zeeblaze/Melodio-SelfMate/Melodio_renders/R5.png

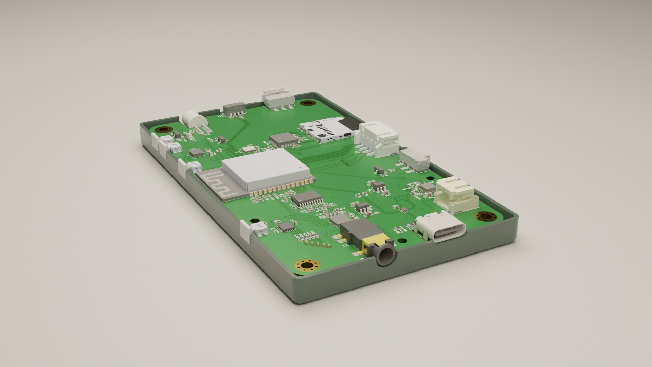
Melodio_renders/R5.png
