zeeblaze/Melodio-SelfMate/Melodio_renders/R6.png

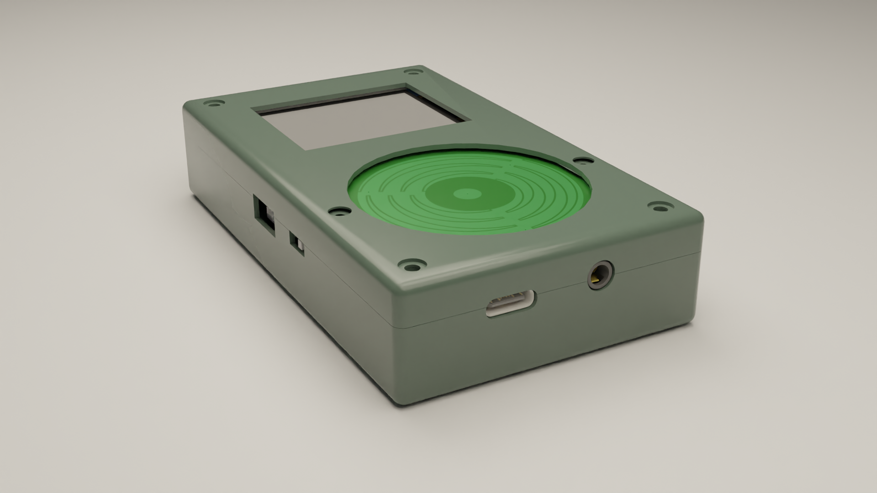
Melodio_renders/R6.png
