zeeblaze/Melodio-SelfMate/Melodio_renders/R7.png

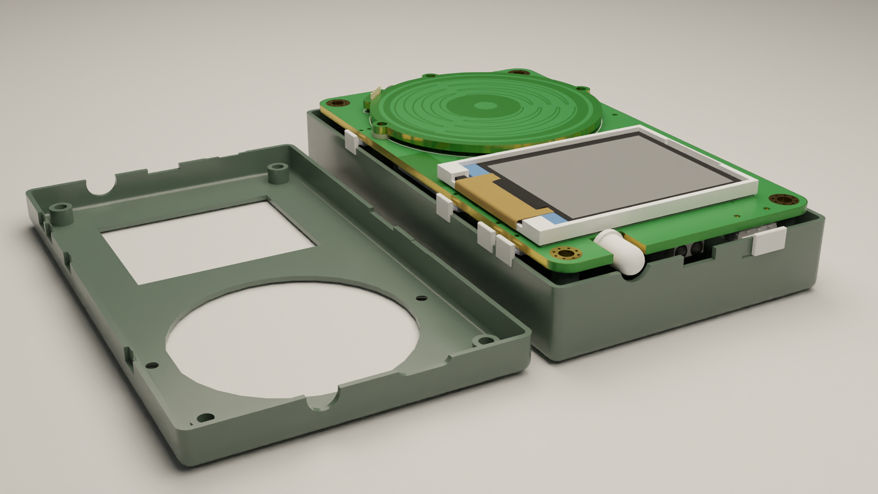
Melodio_renders/R7.png
