zeeblaze/Melodio-SelfMate/Output_PNGs/clickwheel_F_Cu.png

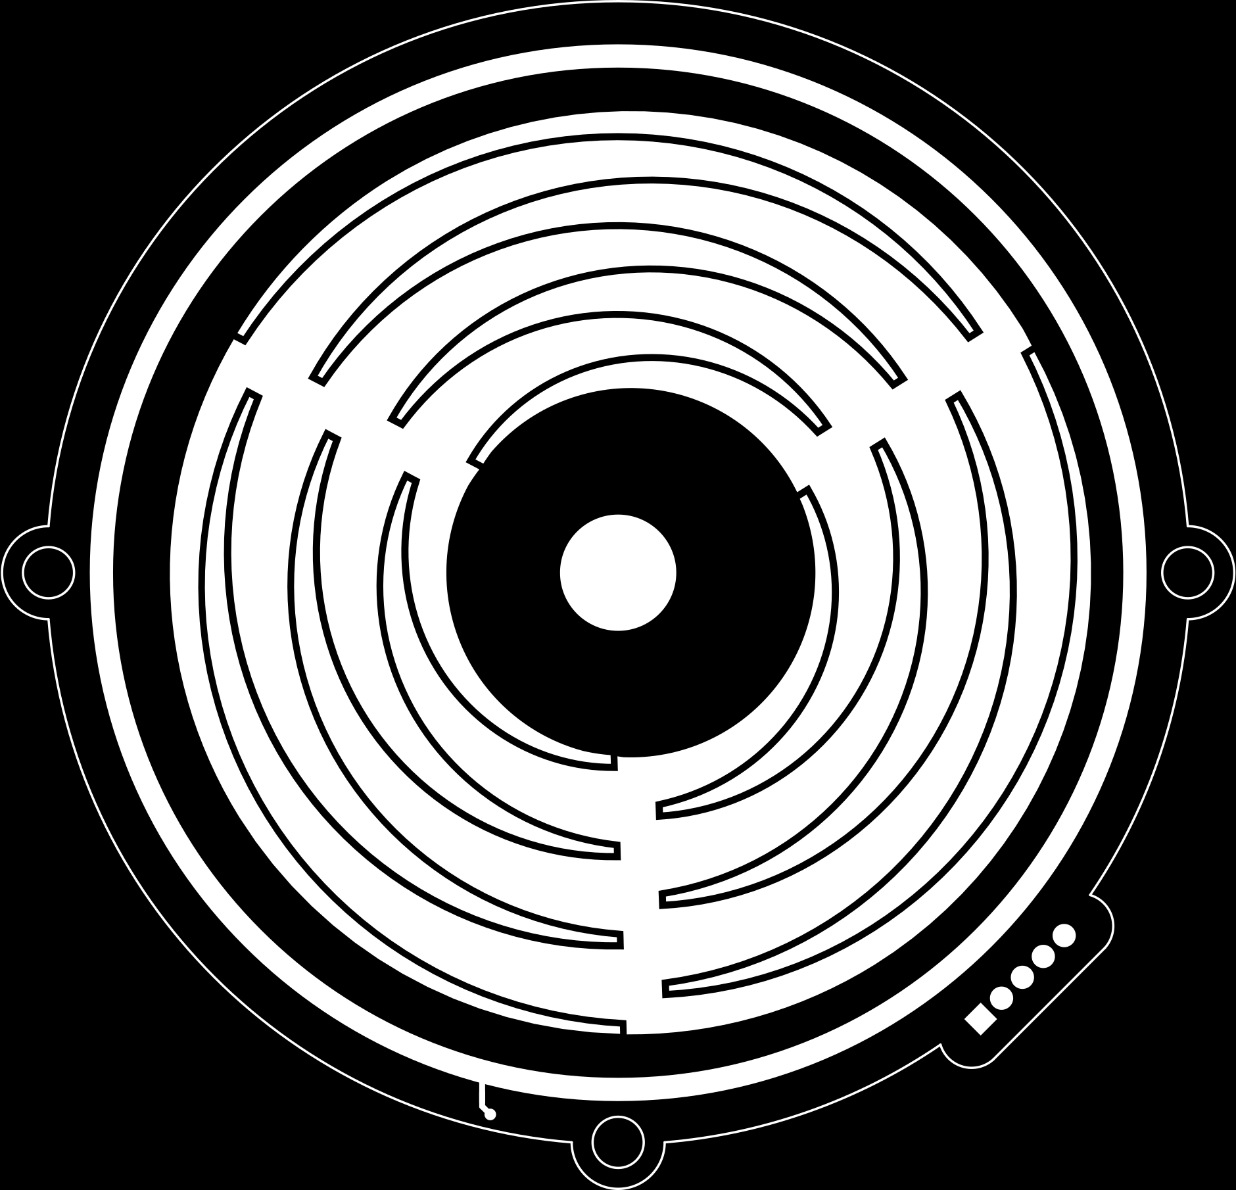
Output_PNGs/clickwheel_F_Cu.png
