zeeblaze/Melodio-SelfMate/Output_PNGs/clickwheel_F_Mask.png

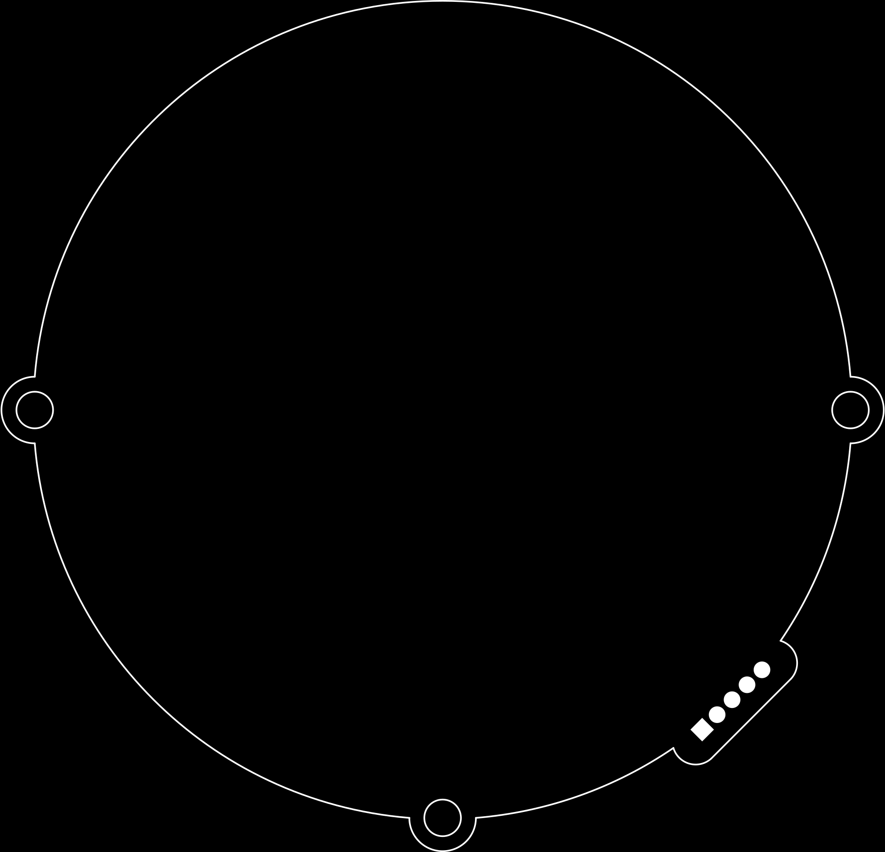
Output_PNGs/clickwheel_F_Mask.png
