zeeblaze/Melodio-SelfMate/Output_PNGs/pcb_B_Mask.png

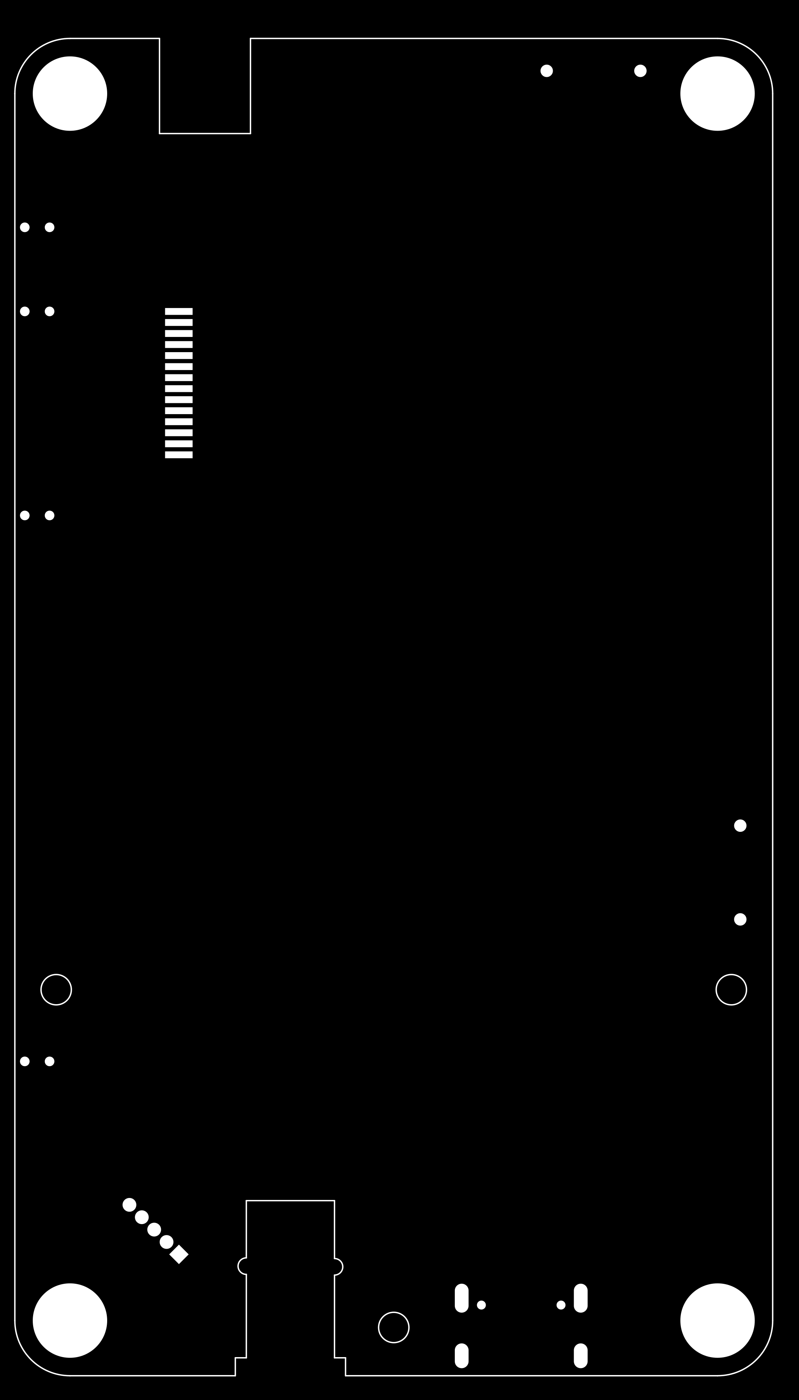
Output_PNGs/pcb_B_Mask.png
