zeeblaze/Melodio-SelfMate/Output_PNGs/pcb_F_Mask.png

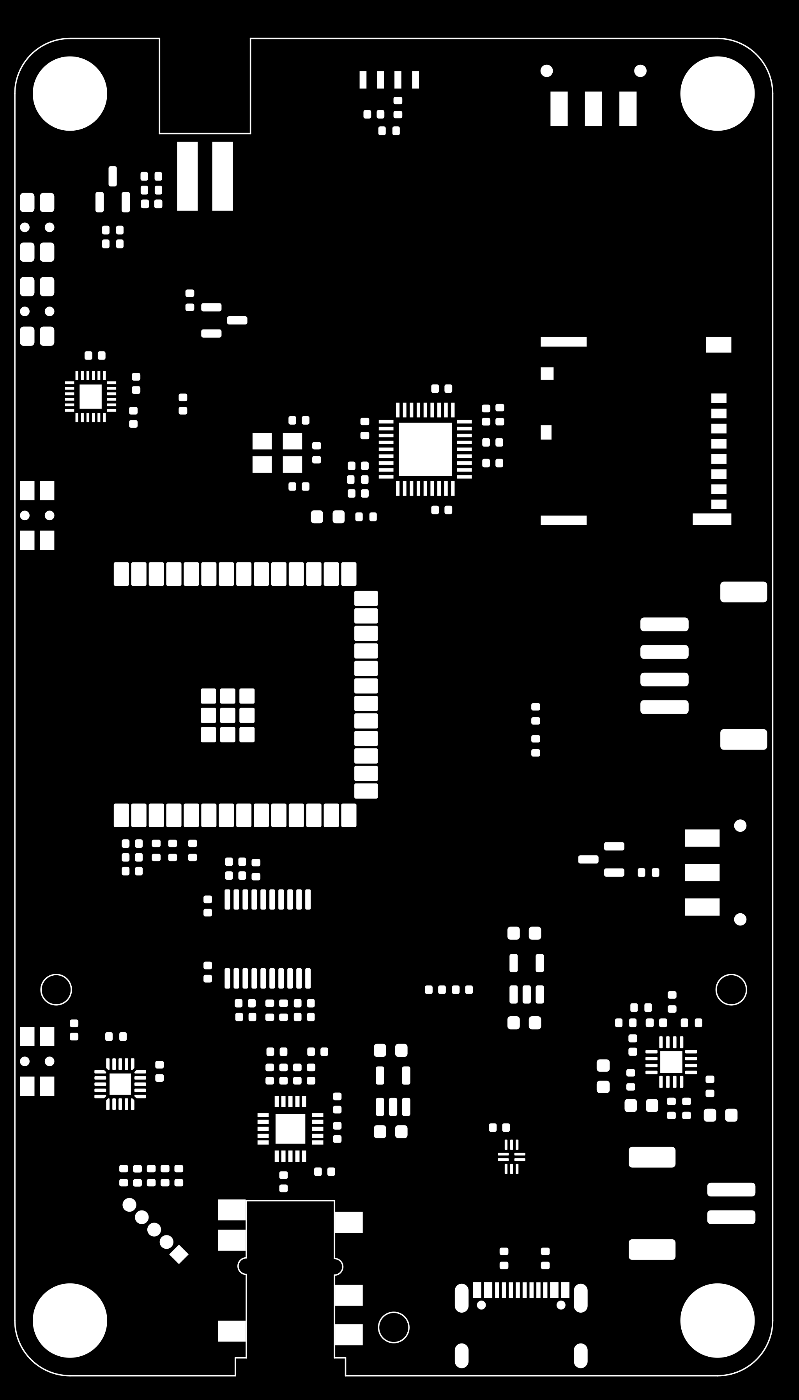
Output_PNGs/pcb_F_Mask.png
