zeeblaze/Melodio-SelfMate/Melodio-SelfMate-V2-3Dmodels/S4B-PH-SM4-TB--3DModel-STEP-56544.STEP

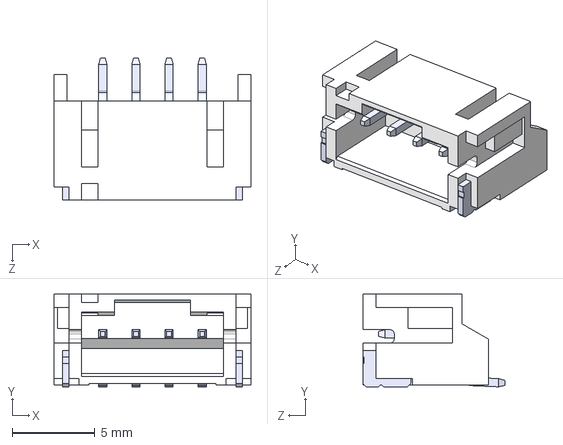
[picture p28: CAD file, 2023-12-09]
Melodio-SelfMate-V2-3Dmodels/S4B-PH-SM4-TB--3DModel-STEP-56544.STEP
11.9 x 5.60 x 8.60 mm
