zeeblaze/Melodio-SelfMate/Melodio-SelfMate-V2-3Dmodels/BQ24075RGTRG4.stp

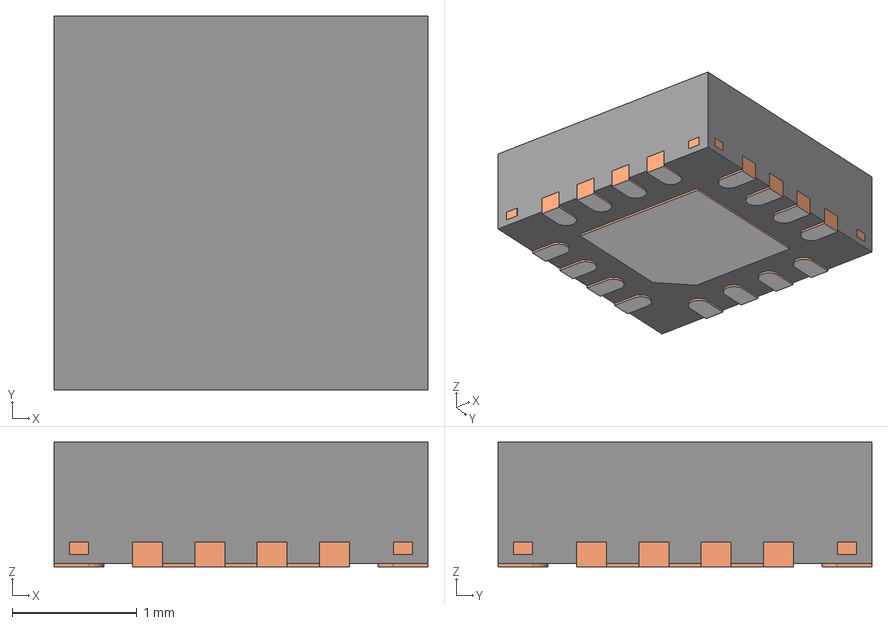
[picture p29: CAD file, 2023-12-09]
Melodio-SelfMate-V2-3Dmodels/BQ24075RGTRG4.stp
3.00 x 3.00 x 1.00 mm
BODY-QFN
FRAME-RGT0016C
PIN1-ID
