zeeblaze/Melodio-SelfMate/Melodio-SelfMate-V2-3Dmodels/503398-1892.step

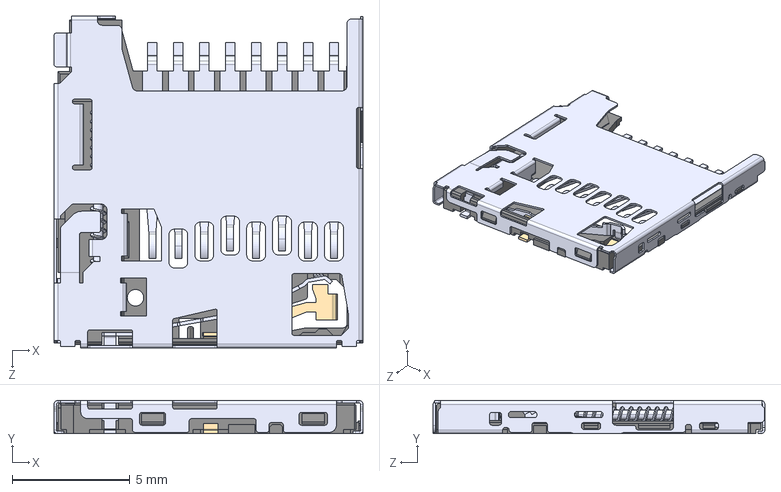
[picture p30: CAD file, 2023-12-09]
Melodio-SelfMate-V2-3Dmodels/503398-1892.step
13.1 x 1.40 x 14.1 mm
