zeeblaze/Melodio-SelfMate/Melodio-SelfMate-V2-3Dmodels/JS102011SAQN--3DModel-Eagle-1.STEP

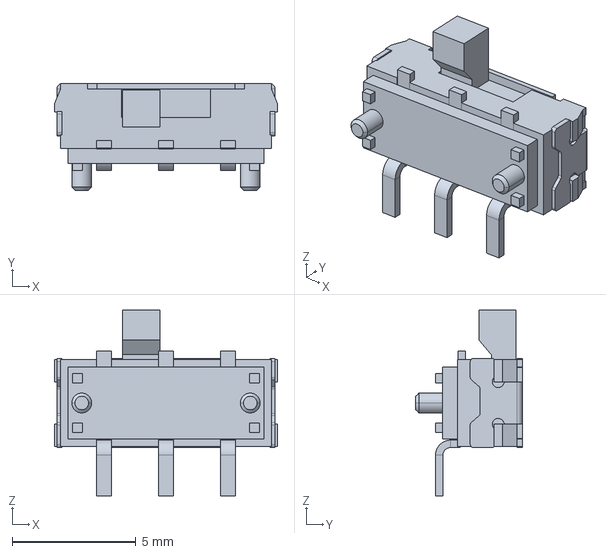
[picture p31: CAD file, 2023-12-09]
Melodio-SelfMate-V2-3Dmodels/JS102011SAQN--3DModel-Eagle-1.STEP
9.00 x 4.30 x 7.50 mm
